hughesjs/tft-dash-essentials/display/assets/themes/default/giraffe.png

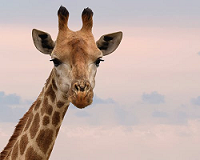
display/assets/themes/default/giraffe.png
