hughesjs/tft-dash-essentials/display/assets/themes/blue/Coolantfantemp.png

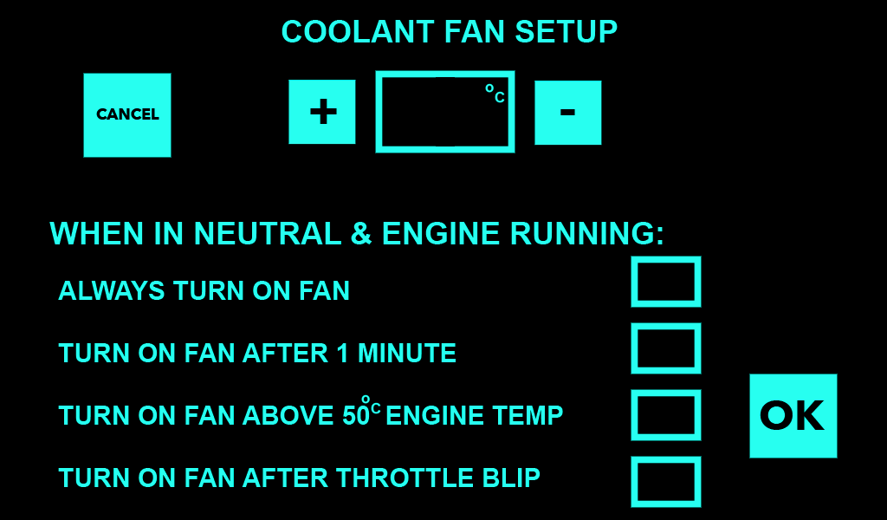
display/assets/themes/blue/Coolantfantemp.png
