hughesjs/tft-dash-essentials/display/assets/themes/blue/Gear.png

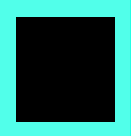
display/assets/themes/blue/Gear.png
