hughesjs/tft-dash-essentials/display/assets/themes/blue/Indicateboth.png

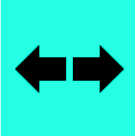
display/assets/themes/blue/Indicateboth.png
