hughesjs/tft-dash-essentials/display/assets/themes/blue/Indicateleft.png

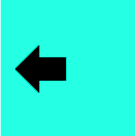
display/assets/themes/blue/Indicateleft.png
