hughesjs/tft-dash-essentials/display/assets/themes/blue/Infobottom.png

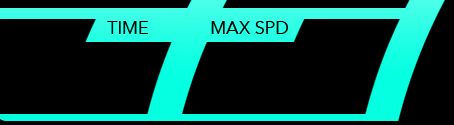
display/assets/themes/blue/Infobottom.png
