hughesjs/tft-dash-essentials/display/assets/themes/blue/Lightoptions.png

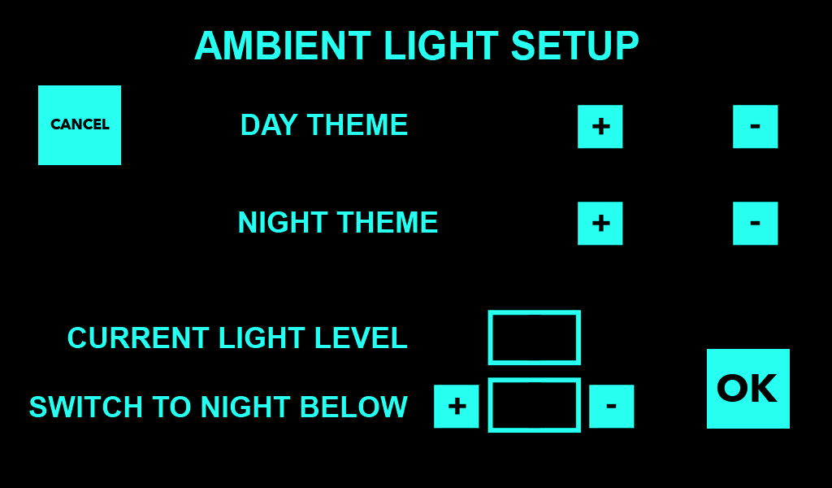
display/assets/themes/blue/Lightoptions.png
