hughesjs/tft-dash-essentials/display/assets/themes/blue/Menuoptionsex.png

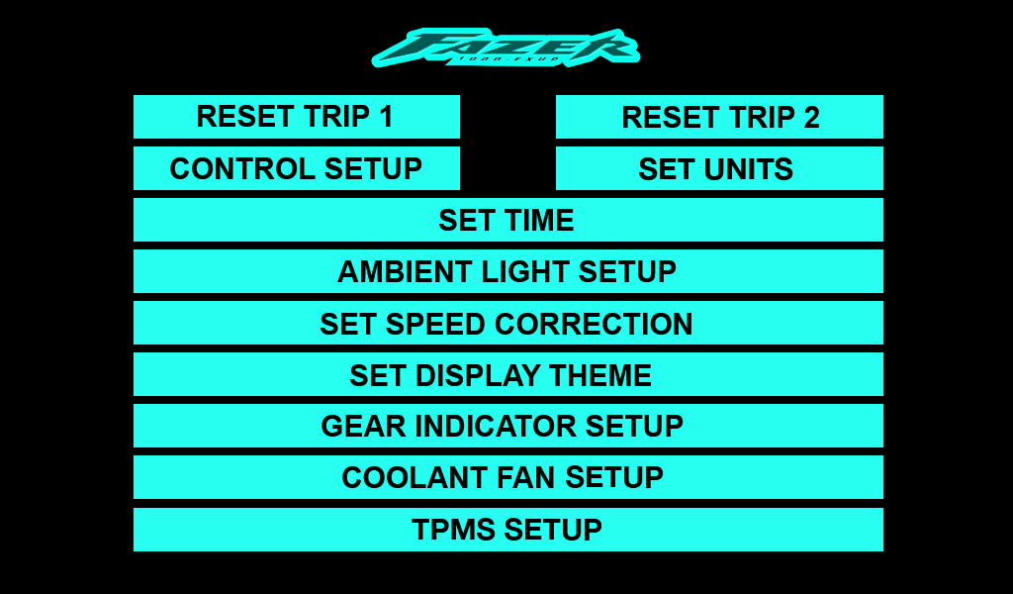
display/assets/themes/blue/Menuoptionsex.png
