hughesjs/tft-dash-essentials/display/assets/themes/blue/Navgfx.png

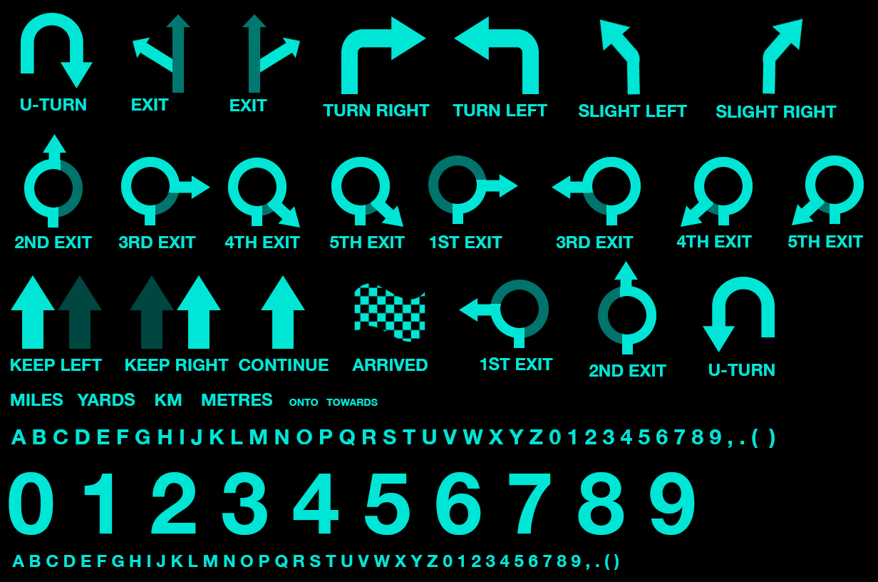
display/assets/themes/blue/Navgfx.png
