hughesjs/tft-dash-essentials/display/assets/themes/blue/Neutrallight.png

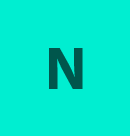
display/assets/themes/blue/Neutrallight.png
