hughesjs/tft-dash-essentials/display/assets/themes/blue/OillightOP.png

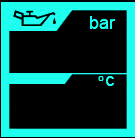
display/assets/themes/blue/OillightOP.png
