hughesjs/tft-dash-essentials/display/assets/themes/bright/Controloptions.png

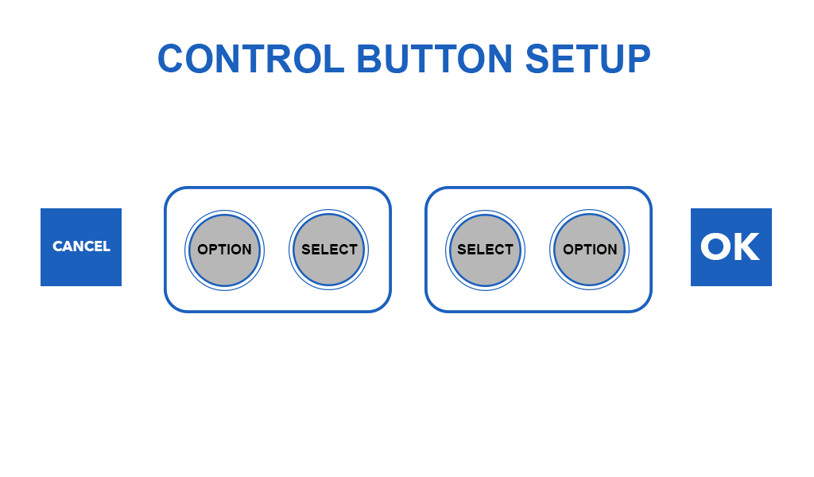
display/assets/themes/bright/Controloptions.png
