hughesjs/tft-dash-essentials/display/assets/themes/bright/Coolantfantemp.png

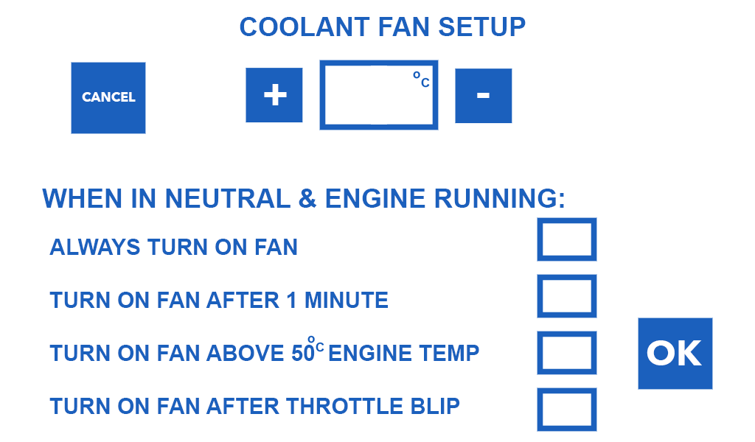
display/assets/themes/bright/Coolantfantemp.png
