hughesjs/tft-dash-essentials/display/assets/themes/bright/Indicateright.png

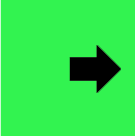
display/assets/themes/bright/Indicateright.png
