hughesjs/tft-dash-essentials/display/assets/themes/bright/Infobottomdiag.png

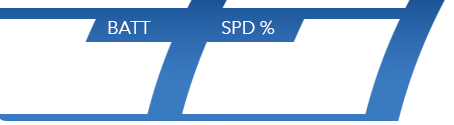
display/assets/themes/bright/Infobottomdiag.png
