hughesjs/tft-dash-essentials/display/assets/themes/bright/Lightoptions.png

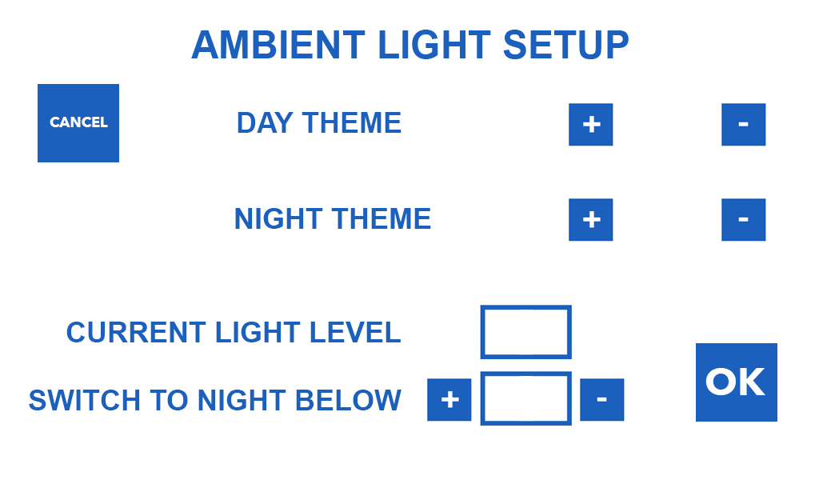
display/assets/themes/bright/Lightoptions.png
