hughesjs/tft-dash-essentials/display/assets/themes/bright/Menuoptionsextpms.png

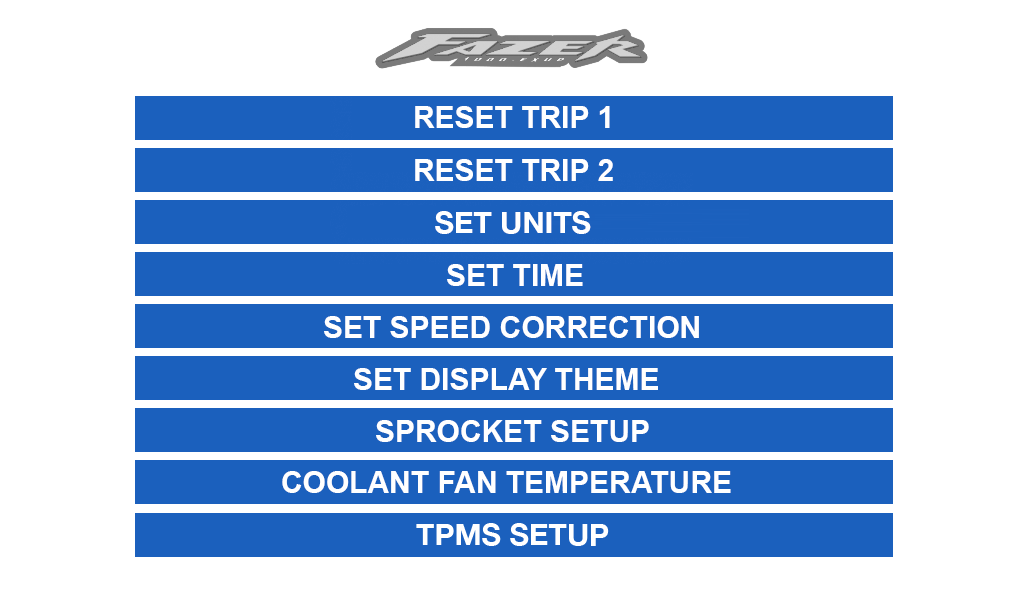
display/assets/themes/bright/Menuoptionsextpms.png
