hughesjs/tft-dash-essentials/display/assets/themes/bright/Oillight.png

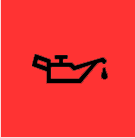
display/assets/themes/bright/Oillight.png
