hughesjs/tft-dash-essentials/display/assets/themes/bright/OillightOP.png

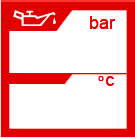
display/assets/themes/bright/OillightOP.png
