hughesjs/tft-dash-essentials/display/assets/themes/bright/Revline.png

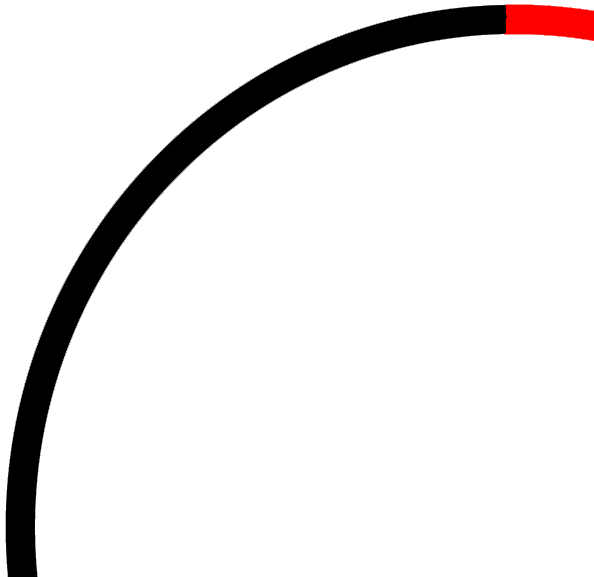
display/assets/themes/bright/Revline.png
