hughesjs/tft-dash-essentials/display/assets/themes/bright/Settime.png

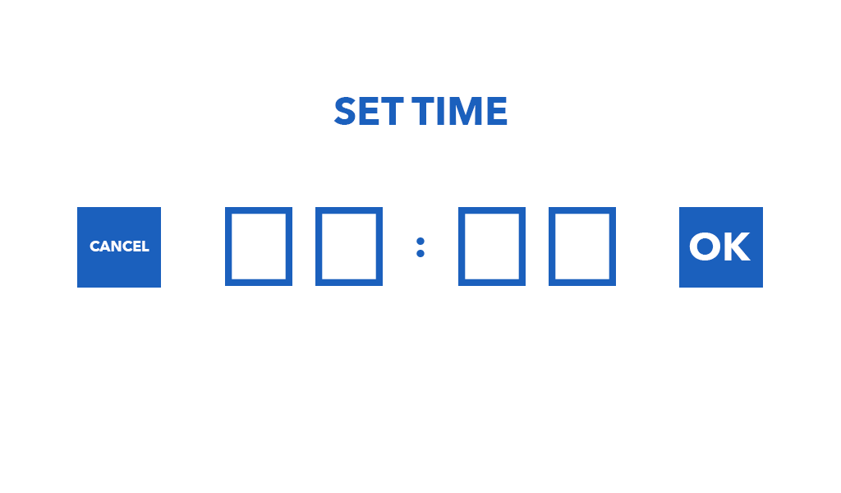
display/assets/themes/bright/Settime.png
