hughesjs/tft-dash-essentials/display/assets/themes/bright/Speedcorrection.png

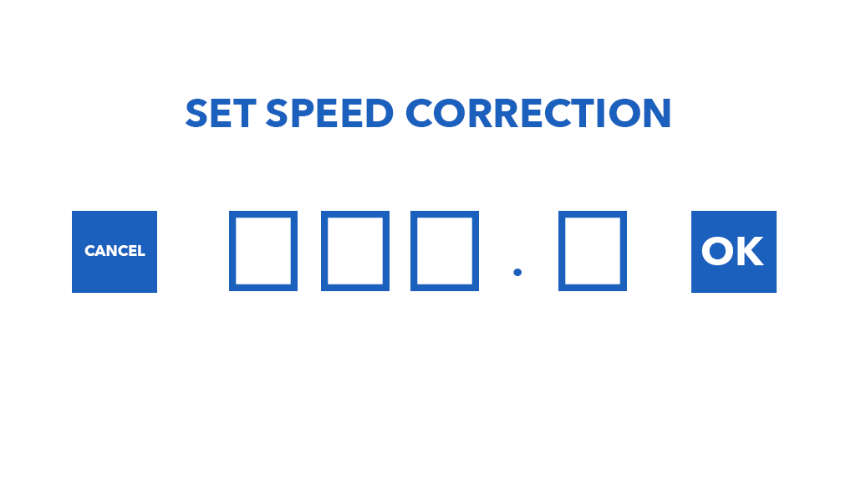
display/assets/themes/bright/Speedcorrection.png
