hughesjs/tft-dash-essentials/display/assets/themes/bright/tyrebottom.png

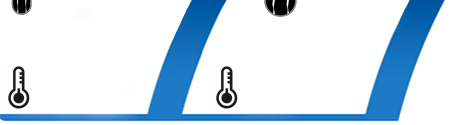
display/assets/themes/bright/tyrebottom.png
