hughesjs/tft-dash-essentials/display/assets/themes/dark/Controloptions.png

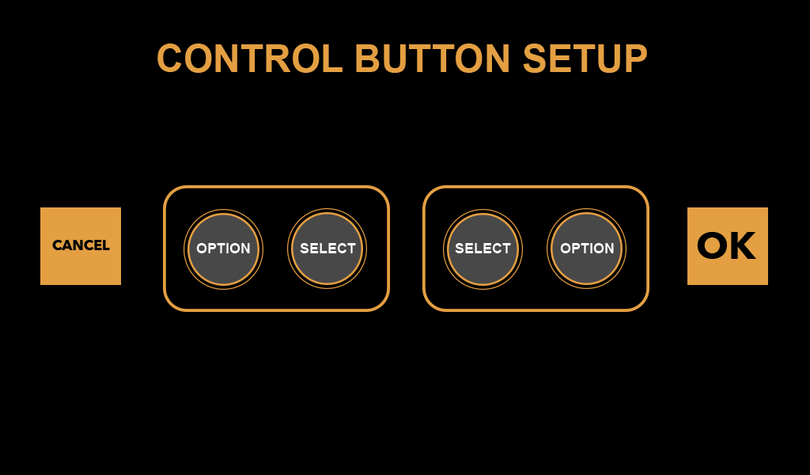
display/assets/themes/dark/Controloptions.png
