hughesjs/tft-dash-essentials/display/assets/themes/dark/Highbeamlight.png

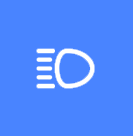
display/assets/themes/dark/Highbeamlight.png
