hughesjs/tft-dash-essentials/display/assets/themes/dark/Mileinfo.png

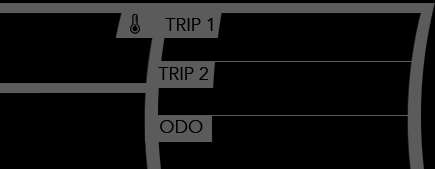
display/assets/themes/dark/Mileinfo.png
