hughesjs/tft-dash-essentials/display/assets/themes/dark/Navbg.png

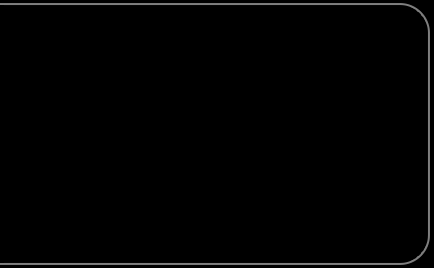
display/assets/themes/dark/Navbg.png
