hughesjs/tft-dash-essentials/display/assets/themes/dark/Oillight.png

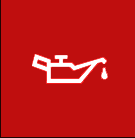
display/assets/themes/dark/Oillight.png
