hughesjs/tft-dash-essentials/display/assets/themes/dark/Setunits.png

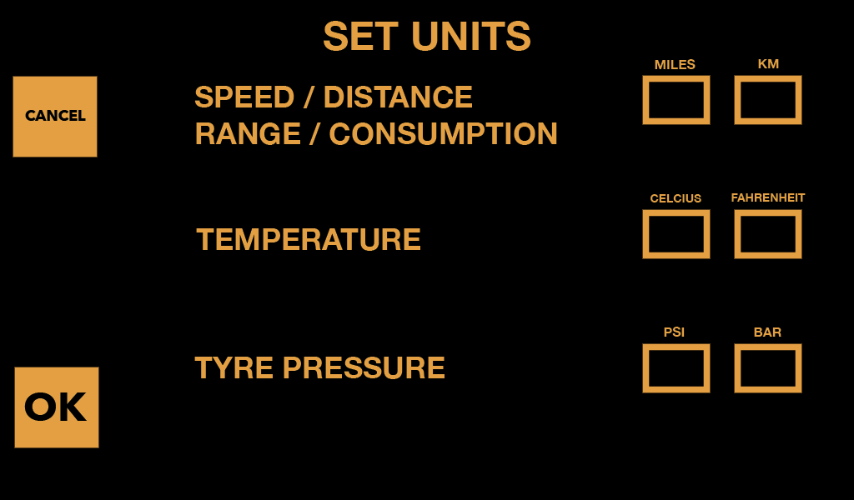
display/assets/themes/dark/Setunits.png
