hughesjs/tft-dash-essentials/display/assets/themes/dark/tyrebottom.png

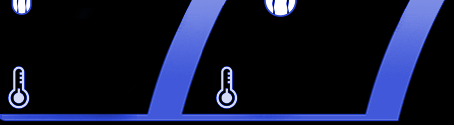
display/assets/themes/dark/tyrebottom.png
