hughesjs/tft-dash-essentials/display/assets/themes/default/Gear.png

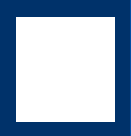
display/assets/themes/default/Gear.png
