hughesjs/tft-dash-essentials/display/assets/themes/default/Menuoptions.png

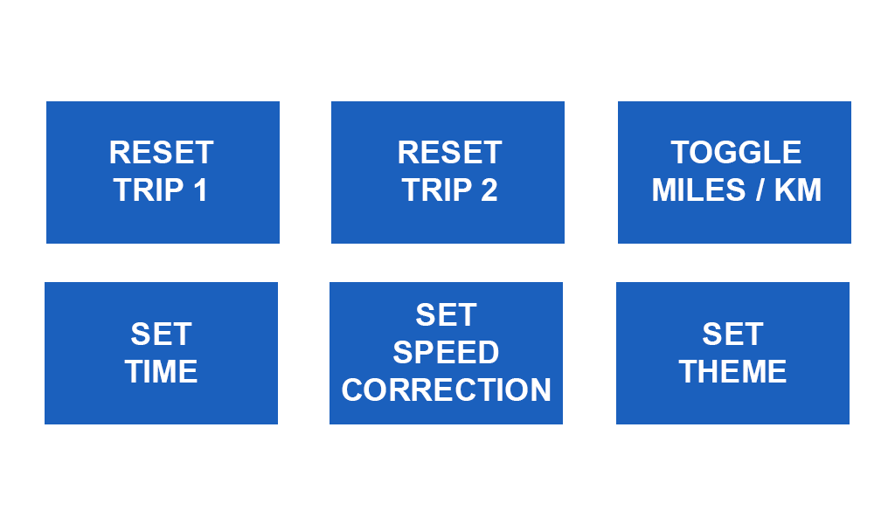
display/assets/themes/default/Menuoptions.png
