hughesjs/tft-dash-essentials/display/assets/themes/default/Menuoptionsex.png

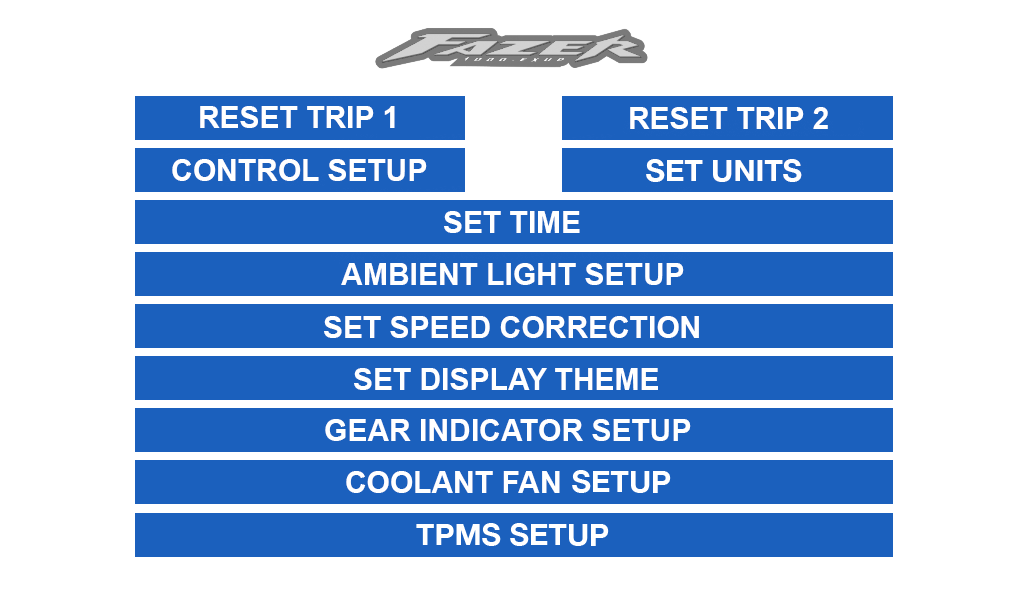
display/assets/themes/default/Menuoptionsex.png
