hughesjs/tft-dash-essentials/display/assets/themes/default/Mileinfo.png

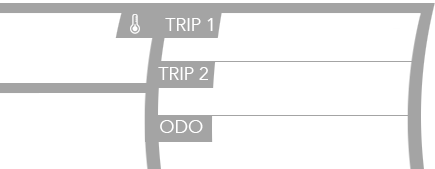
display/assets/themes/default/Mileinfo.png
