hughesjs/tft-dash-essentials/display/assets/themes/default/Setodometer.png

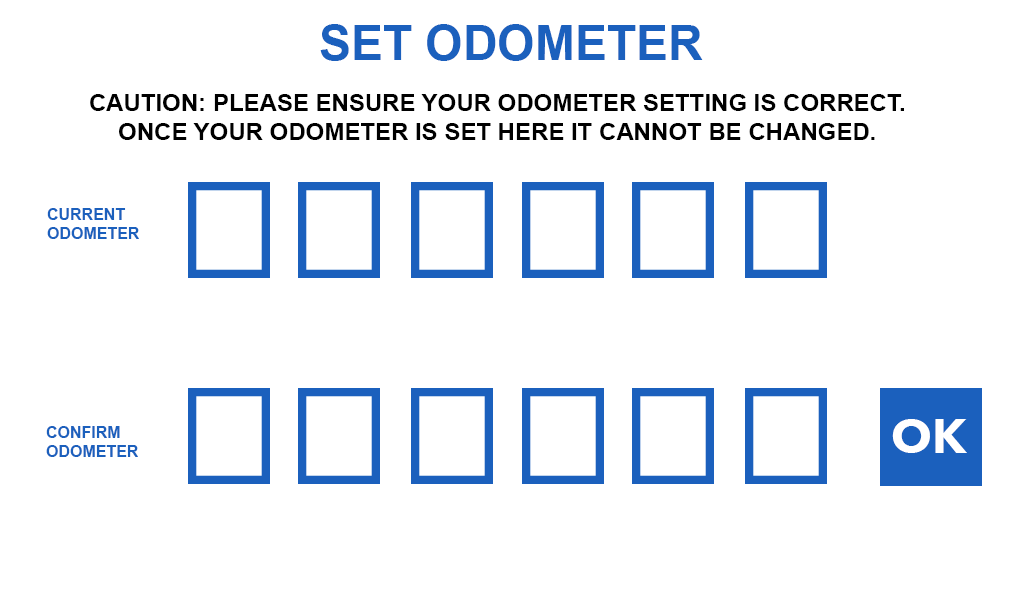
display/assets/themes/default/Setodometer.png
