hughesjs/tft-dash-essentials/display/assets/themes/green/Menuoptions.png

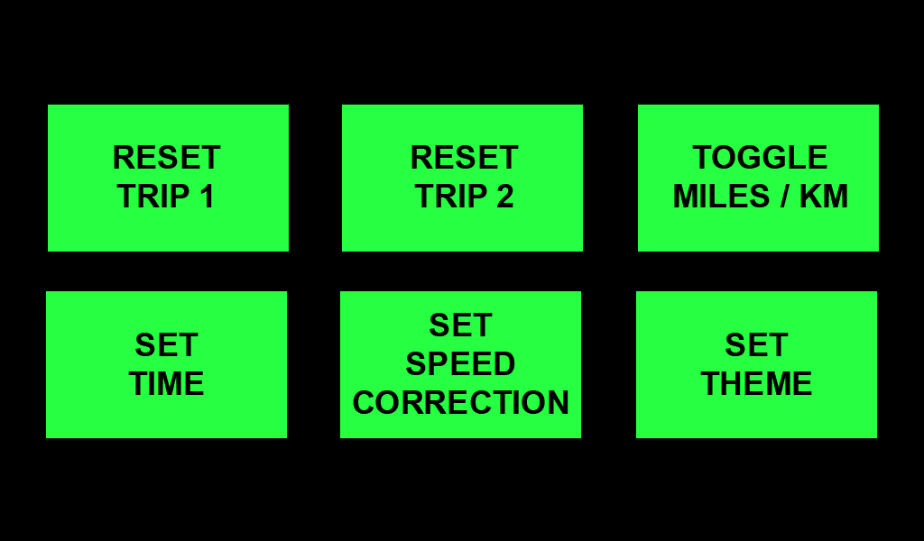
display/assets/themes/green/Menuoptions.png
