hughesjs/tft-dash-essentials/display/assets/themes/green/Speedcorrection.png

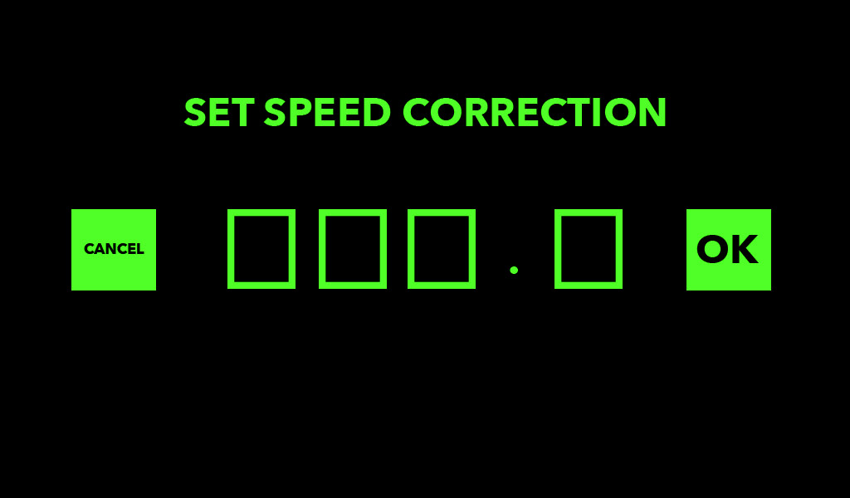
display/assets/themes/green/Speedcorrection.png
