hughesjs/tft-dash-essentials/display/assets/themes/orange/Revline.png

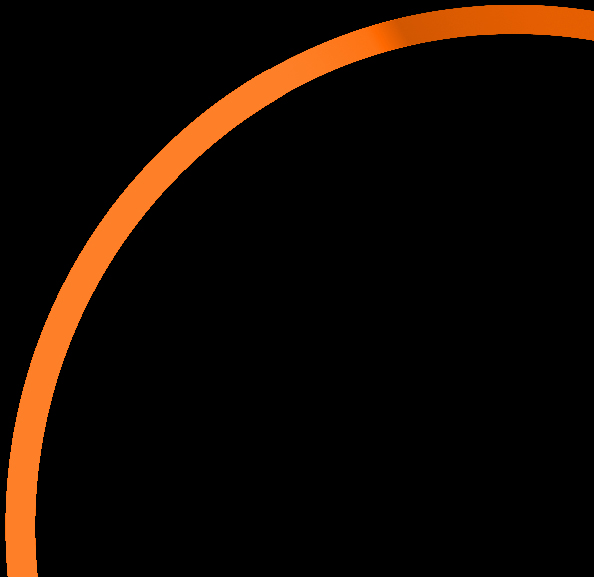
display/assets/themes/orange/Revline.png
