hughesjs/tft-dash-essentials/display/assets/themes/yellow/Controloptions.png

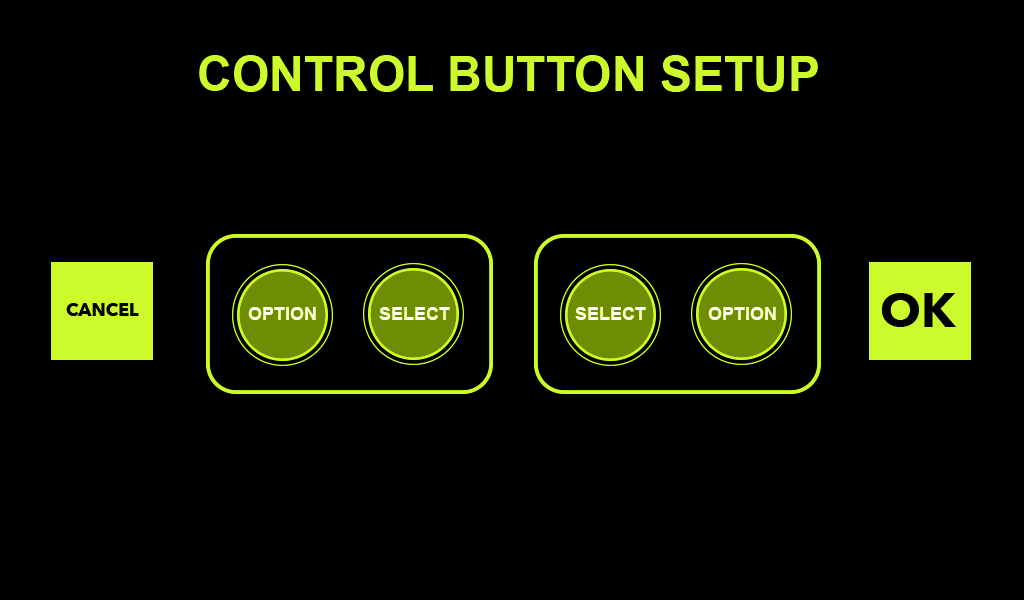
display/assets/themes/yellow/Controloptions.png
