hughesjs/tft-dash-essentials/display/assets/themes/blue/Sprocketsetup.png

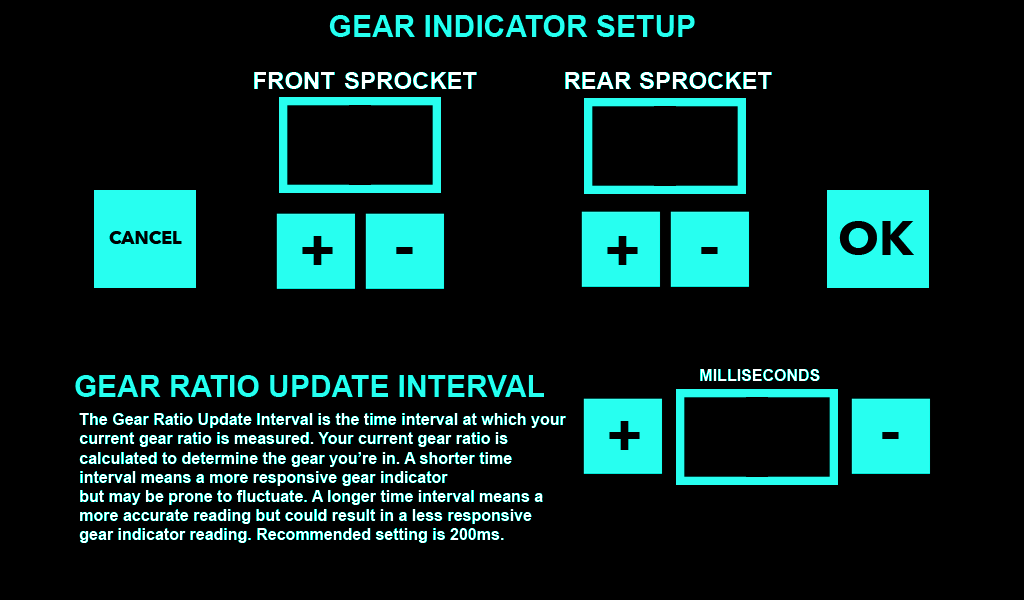
display/assets/themes/blue/Sprocketsetup.png
