hughesjs/tft-dash-essentials/display/assets/themes/blue/TPMSsetup.png

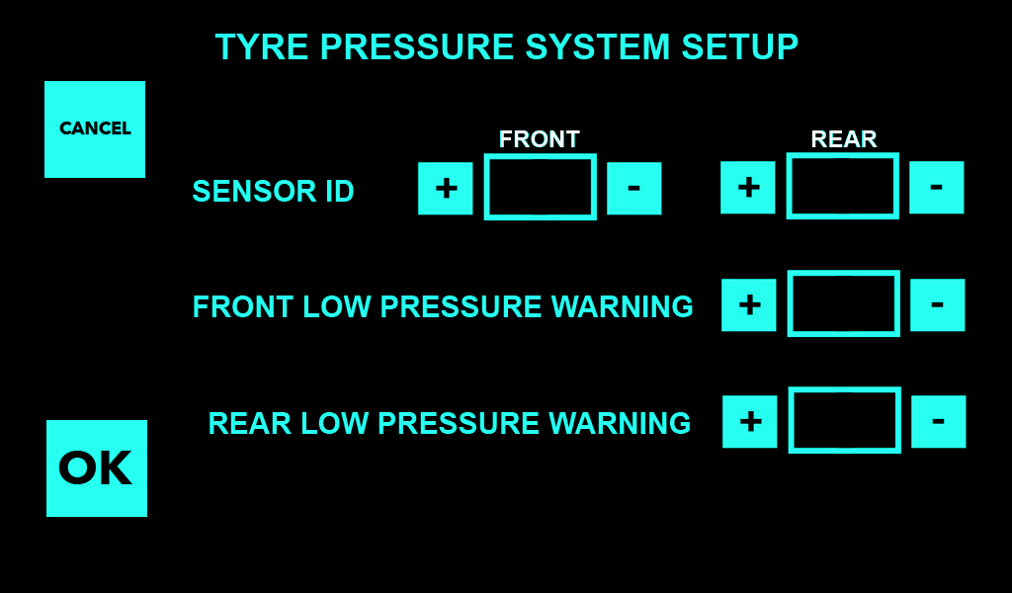
display/assets/themes/blue/TPMSsetup.png
