hughesjs/tft-dash-essentials/display/assets/themes/bright/TPMSsetup.png

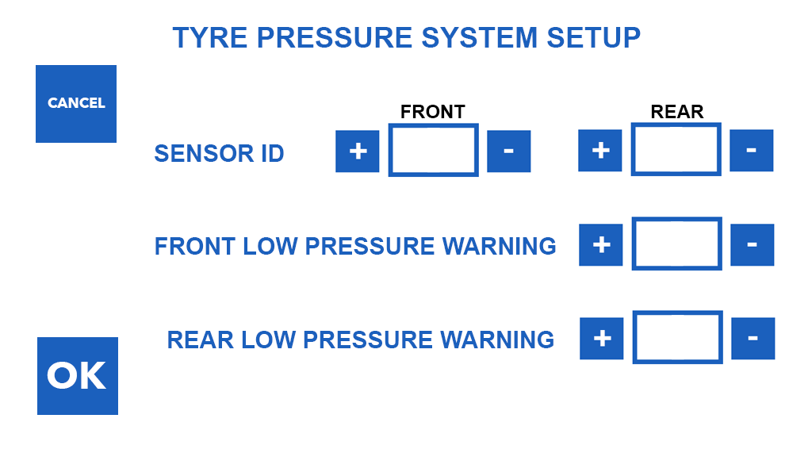
display/assets/themes/bright/TPMSsetup.png
