hughesjs/tft-dash-essentials/display/assets/themes/red/Sprocketsetup.png

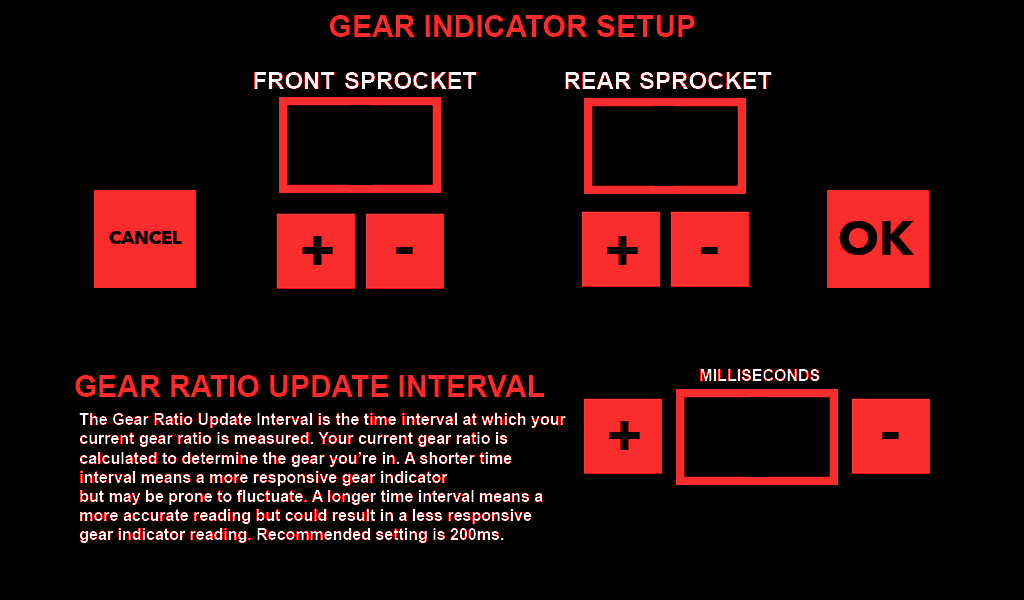
display/assets/themes/red/Sprocketsetup.png
