hughesjs/tft-dash-essentials/buildroot-tftdash/overlay/boot/config.txt

# TFT Dash — Raspberry Pi 3 boot config
#
# DPI display at 1024x600, optimised for fast boot

# Disable unused interfaces
dtoverlay=pi3-disable-bt
dtoverlay=pi3-disable-wifi
dtparam=i2c_arm=off
dtparam=spi=off
dtparam=audio=on

# SD card overclock
dtoverlay=sdtweak,overclock_50=100

# 64-bit kernel
arm_64bit=1

# Fast boot
boot_delay=0
disable_splash=1

# Force HDMI detection
hdmi_force_hotplug=1

# GPU memory
gpu_mem_256=128
gpu_mem_512=256
gpu_mem_1024=256

# DPI display — 1024x600 @ 60Hz
dtoverlay=dpi24
enable_dpi_lcd=1
display_default_lcd=1
dpi_group=2
dpi_mode=87
dpi_output_format=0x6f005
hdmi_cvt 1024 600 60 6 0 0 0
disable_overscan=1
overscan_scale=1

start_x=0
